sunriax/everblinksolar/EBS.asc

C1: EuropeanPolcap; 1F
C2: cap; 100n
C3: EuropeanPolcap; 10µ
D1: LED; NSCW100
D2: schottky; 1N5817
Q1: npn; BC547C
Q2: pnp; BC557C
R1: Resistor; 10Meg
R2: Resistor; 10Meg
R3: Resistor; 4Meg7
R4: Resistor; 33k
R5: Resistor; 1k
R6: Resistor; 1k
R7: Resistor; 10k
R8: Resistor; 1k
R9: Resistor; 10k
V1: UQuelle_EU; 2V2
Named nets: 0
.tran 10s
